GearBoxFox/foxxboard/PCB/MX_V2-main/3D/Kailh-Choc-Socket-CPG135001S30.step

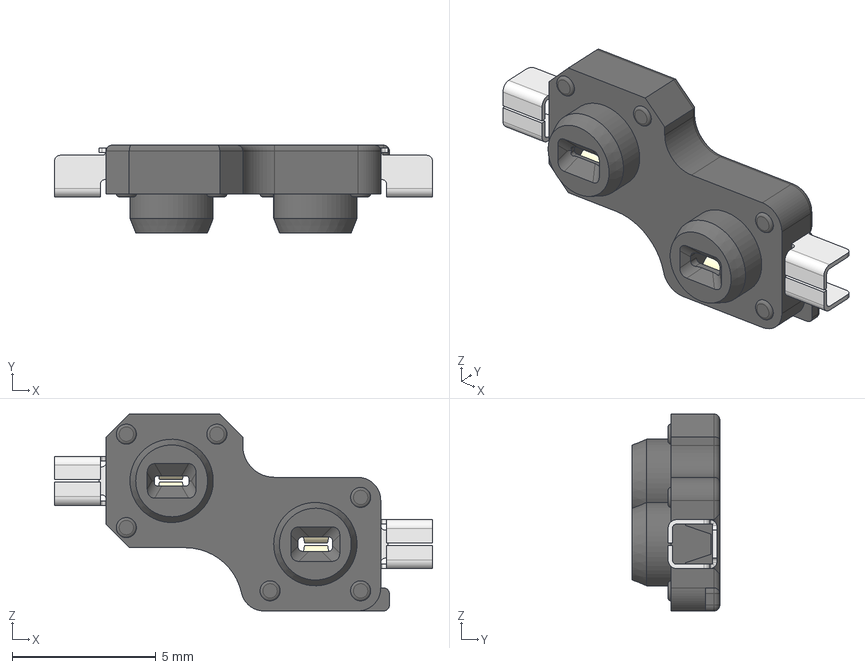
[picture p24: CAD file, 2025-01-30]
PCB/MX_V2-main/3D/Kailh-Choc-Socket-CPG135001S30.step
13.1 x 3.05 x 6.85 mm
Insert 2
Insert 1
