GearBoxFox/foxxboard/PCB/v3/demo.dxf

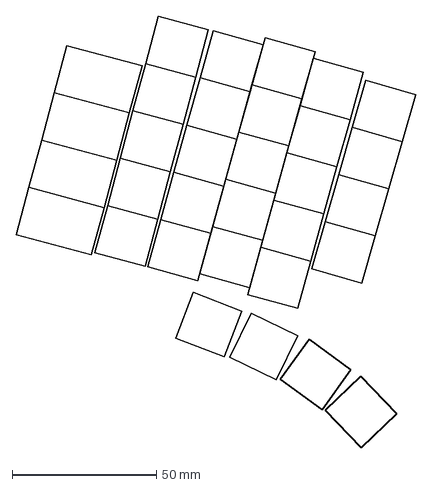
[picture p25: CAD file, 2025-03-09]
PCB/v3/demo.dxf
138.6 x 149.7 mm
