GearBoxFox/foxxboard/PCB/3d/Gateron_ks33_hotswap_socket.step

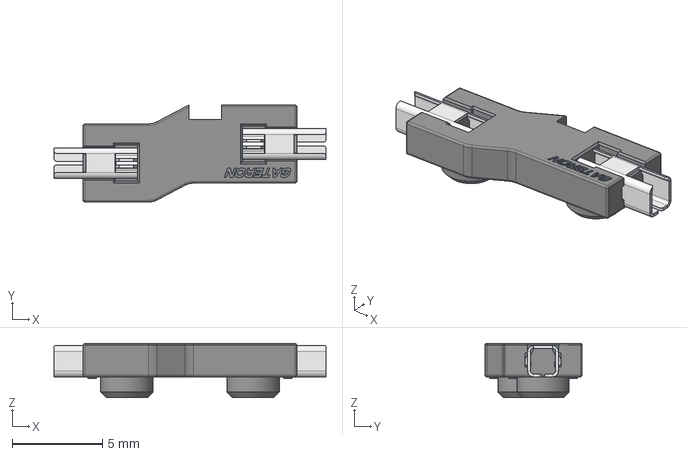
[picture p26: CAD file, 2025-03-09]
PCB/3d/Gateron_ks33_hotswap_socket.step
15.1 x 5.39 x 3.00 mm
