GearBoxFox/foxxboard/PCB/Keebio-Parts/3dmodels/PJ-320A.step

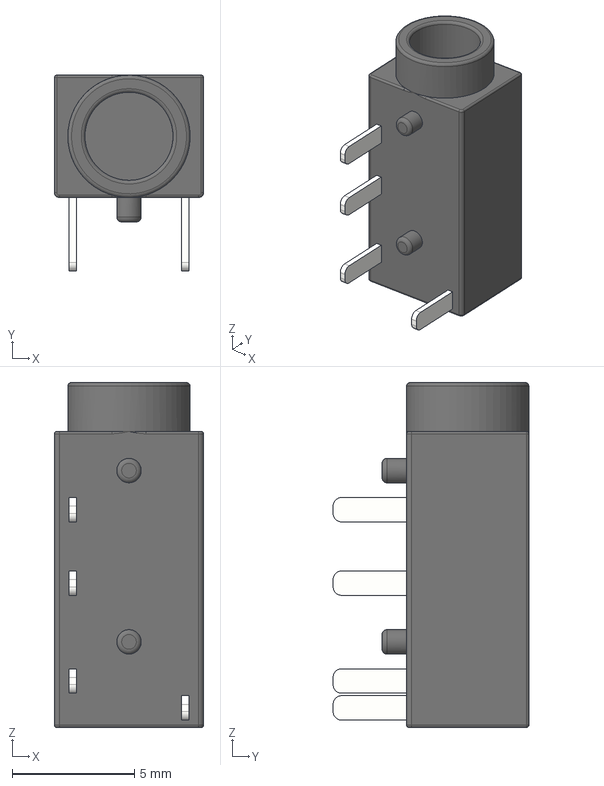
[picture p27: CAD file, 2025-01-30]
PCB/Keebio-Parts/3dmodels/PJ-320A.step
6.10 x 8.00 x 14.1 mm
