GearBoxFox/foxxboard/PCB/v3/v2.dxf

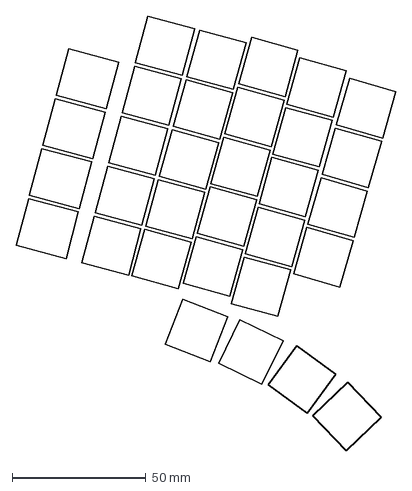
[picture p28: CAD file, 2025-02-07]
PCB/v3/v2.dxf
141.8 x 162.1 mm
