GearBoxFox/foxxboard/PCB/3d/128x32-OLED.STEP

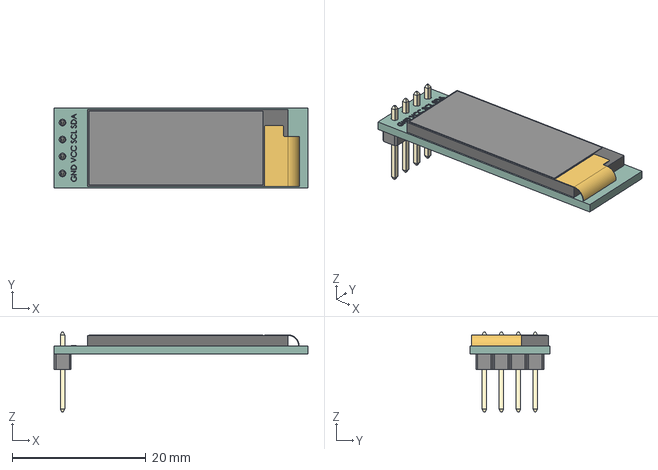
[picture p29: CAD file, 2025-02-07]
PCB/3d/128x32-OLED.STEP
38.0 x 12.0 x 11.9 mm
