GearBoxFox/foxxboard/PCB/Keebio-Parts/3dmodels/EC11B-SW-Horiz-15K-blue.step

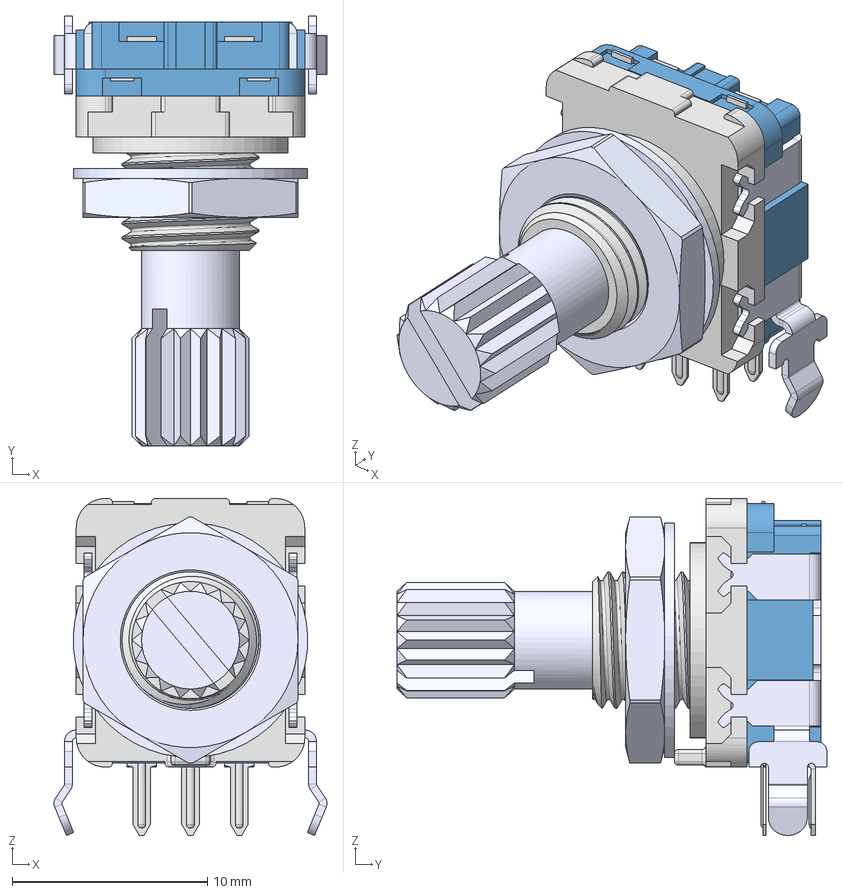
[picture p30: CAD file, 2025-01-30]
PCB/Keebio-Parts/3dmodels/EC11B-SW-Horiz-15K-blue.step
14.0 x 22.0 x 17.3 mm
