GearBoxFox/foxxboard/PCB/Keebio-Parts/Keebio-Parts.pretty-master/3dmodels/SK6812MINI-E v1.step

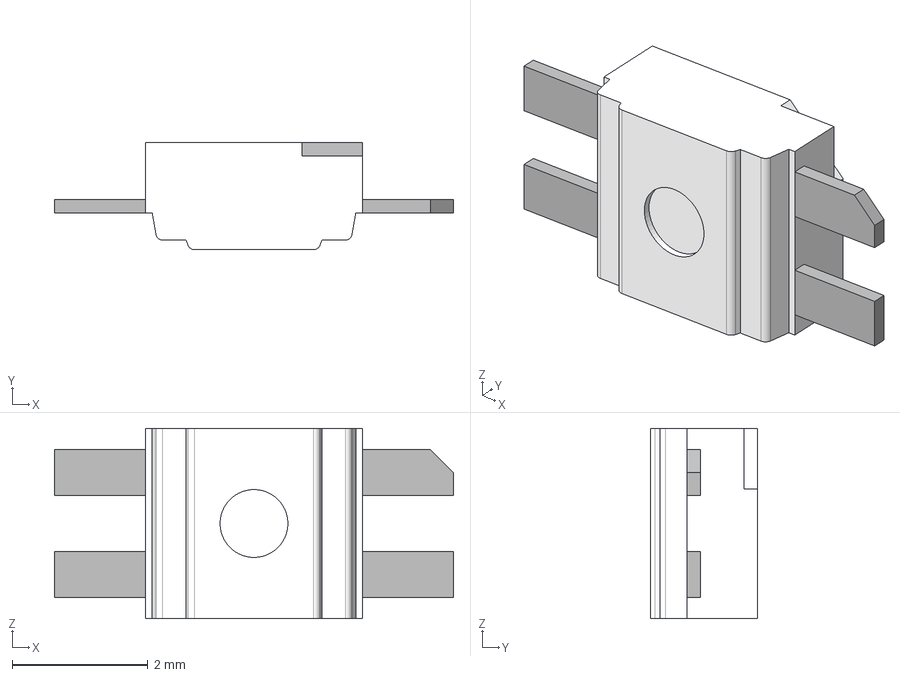
[picture p31: CAD file, 2025-01-30]
PCB/Keebio-Parts/Keebio-Parts.pretty-master/3dmodels/SK6812MINI-E v1.step
5.88 x 1.58 x 2.80 mm
