GearBoxFox/foxxboard/PCB/3d/EC11 Rotary Encoder Dode Switch-15mm .STEP

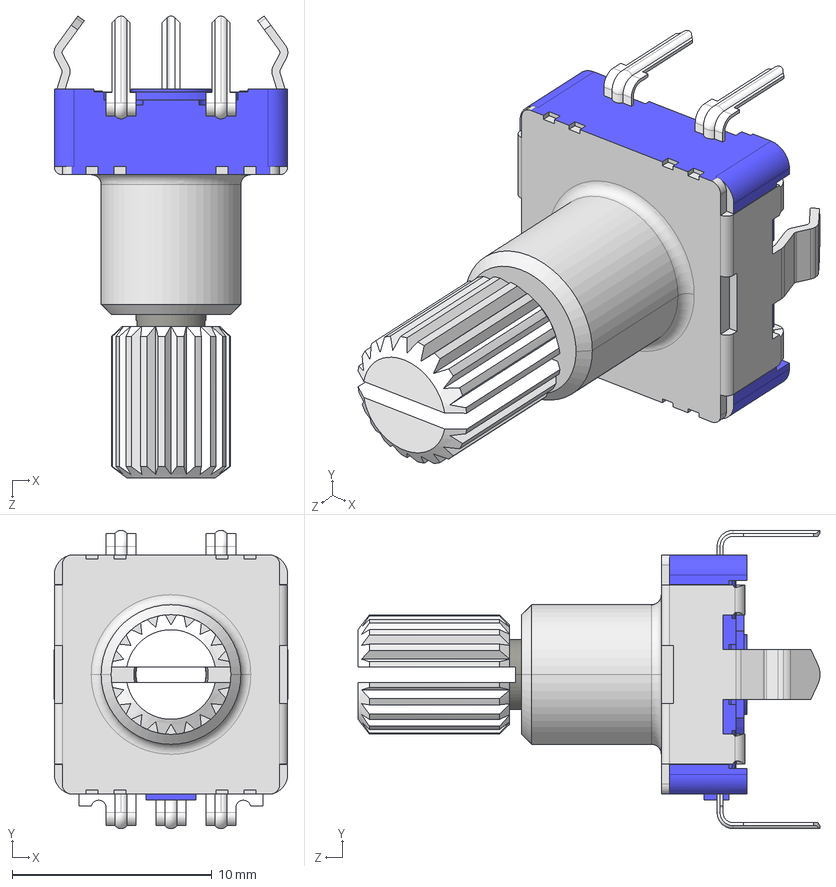
[picture p32: CAD file, 2025-02-07]
PCB/3d/EC11 Rotary Encoder Dode Switch-15mm .STEP
11.7 x 15.0 x 23.2 mm
