GearBoxFox/foxxboard/PCB/3d/[low detail] Low Profile Cherry MX Red.step

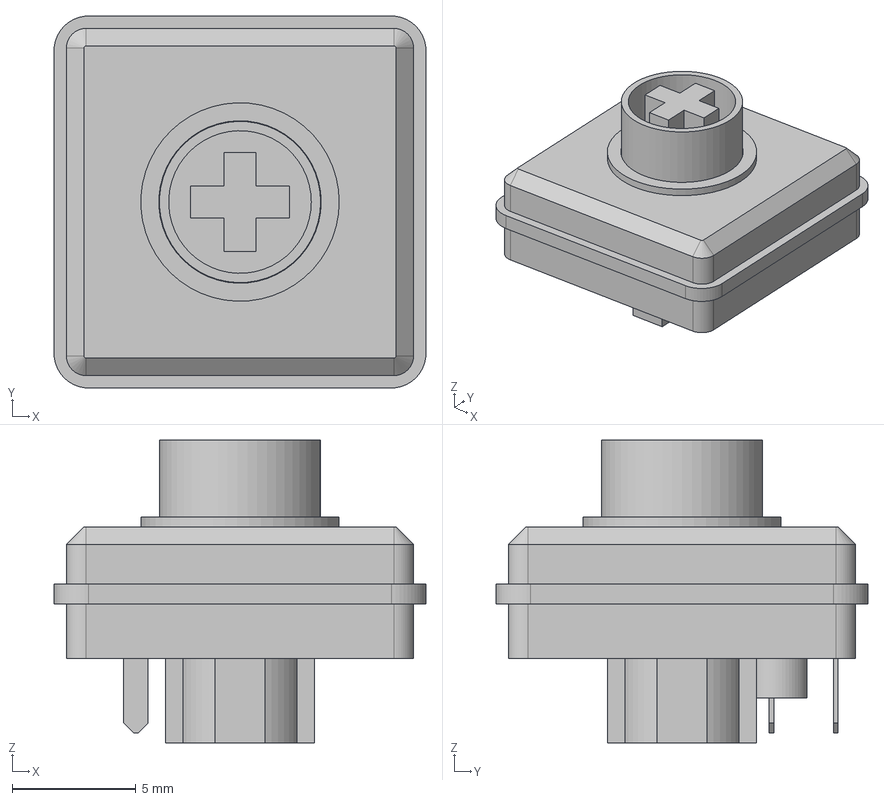
[picture p33: CAD file, 2025-02-07]
PCB/3d/[low detail] Low Profile Cherry MX Red.step
15.0 x 15.0 x 12.2 mm
