GearBoxFox/foxxboard/PCB/3d/Cherry MX.STEP

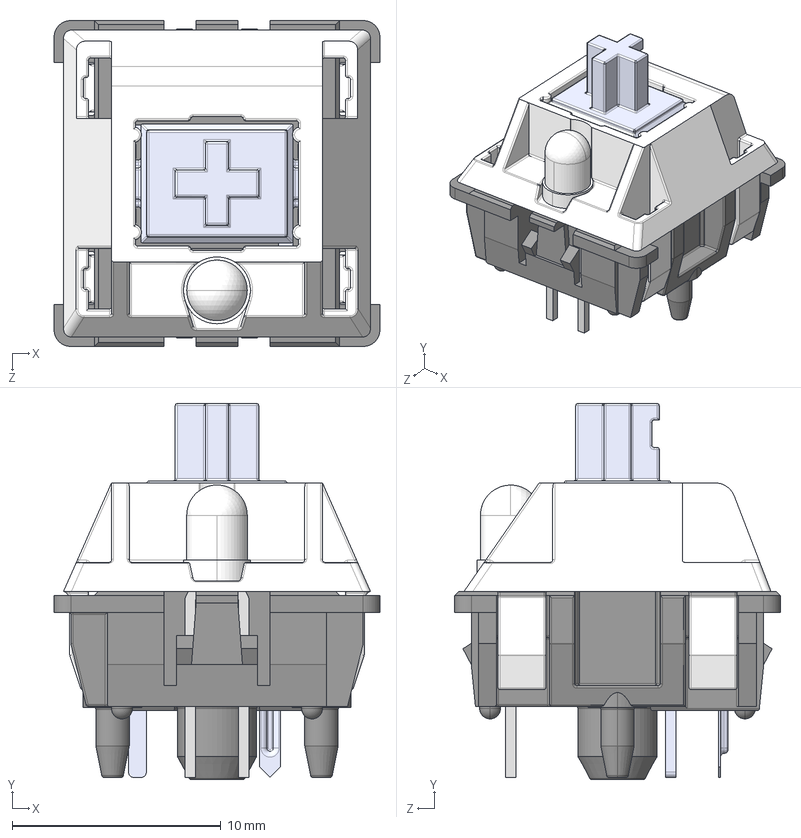
[picture p34: CAD file, 2025-02-07]
PCB/3d/Cherry MX.STEP
15.6 x 18.0 x 15.6 mm
Bottom
Pulsador
Top
Pieza5^Cherry MX
Pin1
Pin2
Led 3mm_trans
